KamuiSW/MP-SolarBot/Software/src/Training/PWS_SolarML_Detection/MLReferences/Dirty/Electrical-damage/Electrical (2).JPG

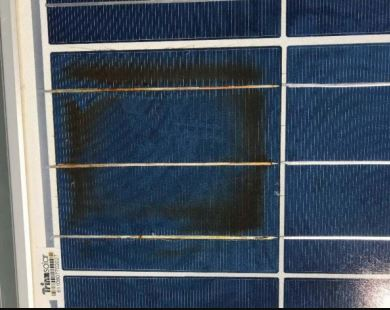
Software/src/Training/PWS_SolarML_Detection/MLReferences/Dirty/Electrical-damage/Electrical (2).JPG
