KamuiSW/MP-SolarBot/PWS_SolarML_Detection/demo_heatmap.jpg

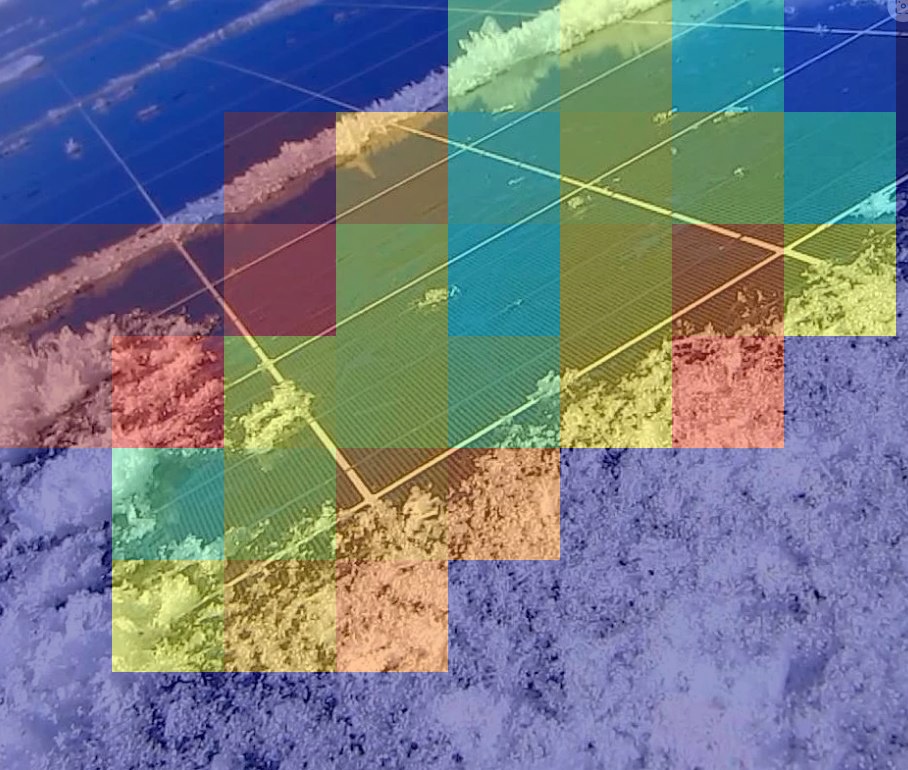
PWS_SolarML_Detection/demo_heatmap.jpg
