KamuiSW/MP-SolarBot/Software/src/Training/PWS_SolarML_Detection/demo_heatmap.jpg

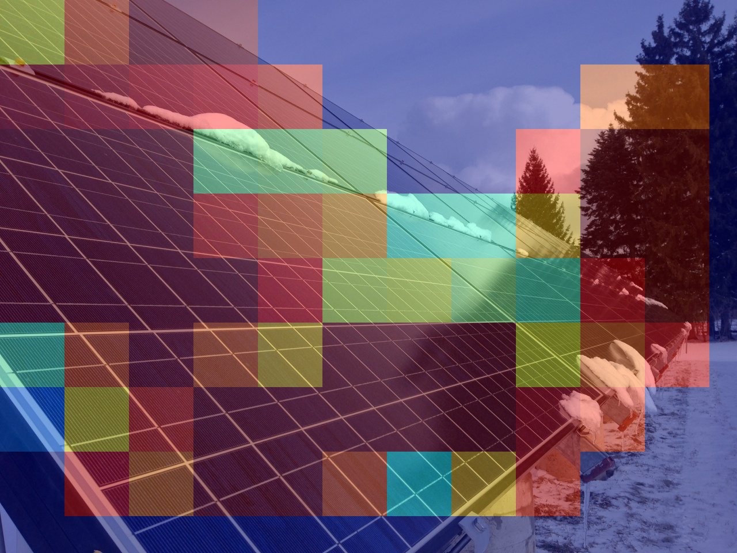
Software/src/Training/PWS_SolarML_Detection/demo_heatmap.jpg
