KamuiSW/MP-SolarBot/Software/src/Training/PWS_SolarML_Detection/MLReferences/Dirty/Bird-drop/New/5.JPG

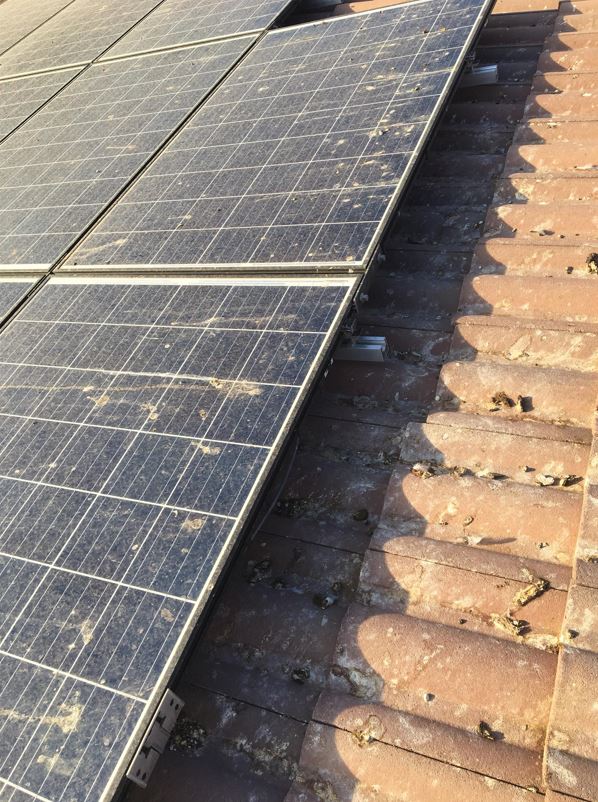
Software/src/Training/PWS_SolarML_Detection/MLReferences/Dirty/Bird-drop/New/5.JPG
