KamuiSW/MP-SolarBot/Software/src/Training/PWS_SolarML_Detection/MLReferences/Dirty/Electrical-damage/Electrical (1).jpg

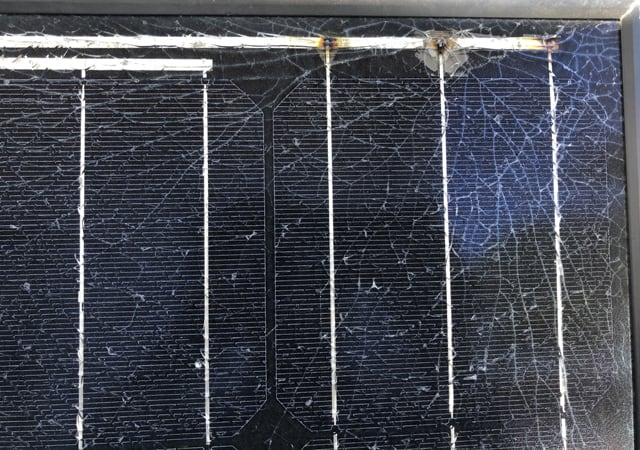
Software/src/Training/PWS_SolarML_Detection/MLReferences/Dirty/Electrical-damage/Electrical (1).jpg
