KamuiSW/MP-SolarBot/Software/src/Training/PWS_SolarML_Detection/MLReferences/Dirty/Electrical-damage/Electrical (2).png

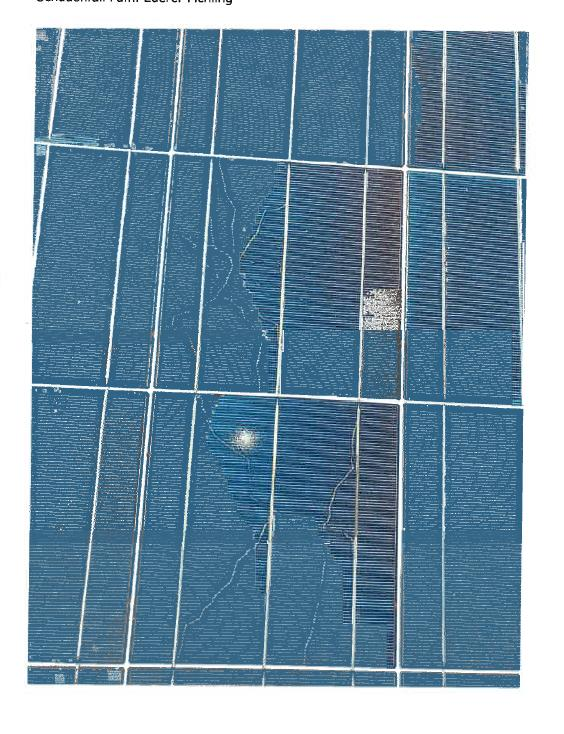
Software/src/Training/PWS_SolarML_Detection/MLReferences/Dirty/Electrical-damage/Electrical (2).png
