KamuiSW/MP-SolarBot/Software/src/Training/PWS_SolarML_Detection/MLReferences/Dirty/Physical-Damage/Physical (2).jpg

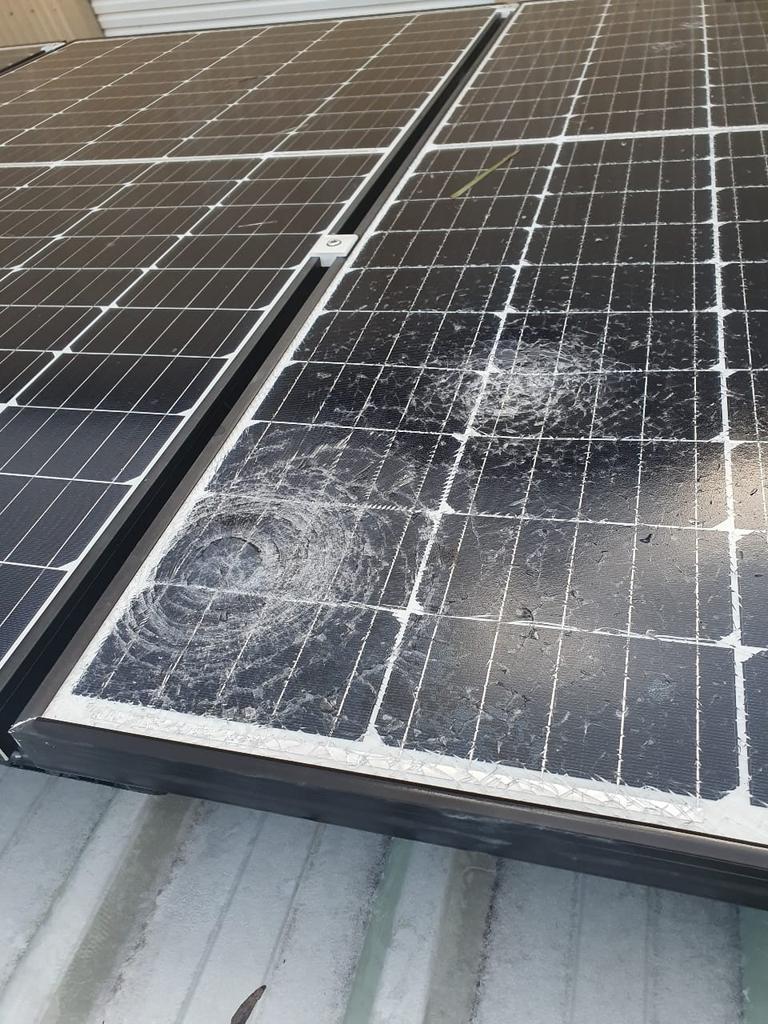
Software/src/Training/PWS_SolarML_Detection/MLReferences/Dirty/Physical-Damage/Physical (2).jpg
