KamuiSW/MP-SolarBot/Software/src/Training/PWS_SolarML_Detection/MLReferences/Dirty/Physical-Damage/Physical (4).jpg

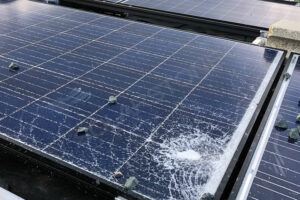
Software/src/Training/PWS_SolarML_Detection/MLReferences/Dirty/Physical-Damage/Physical (4).jpg
