KamuiSW/MP-SolarBot/Software/src/Training/PWS_SolarML_Detection/MLReferences/Dirty/Snow-Covered/Snow (1).jpg

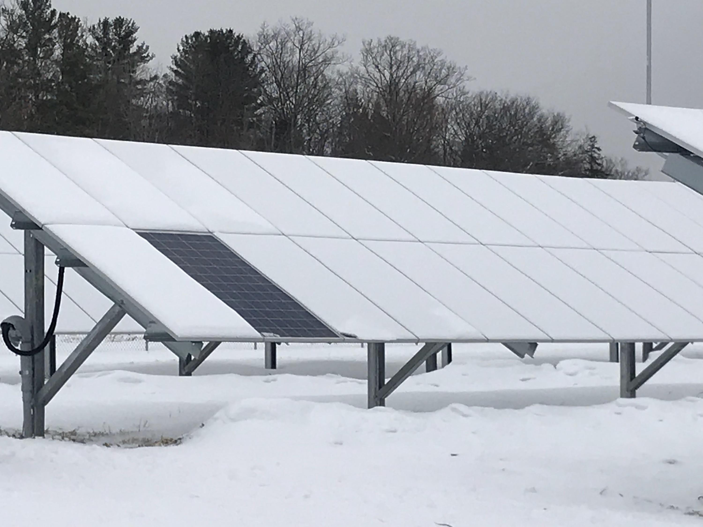
Software/src/Training/PWS_SolarML_Detection/MLReferences/Dirty/Snow-Covered/Snow (1).jpg
